janc18/CAE32/Source_code/Interfaz_grafica/Interfaz_gtk/src_images/Volante2.png

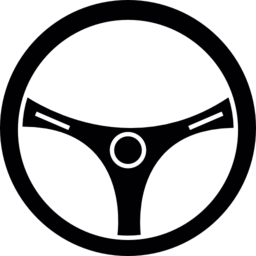
Source_code/Interfaz_grafica/Interfaz_gtk/src_images/Volante2.png
