janc18/CAE32/UML/UML_png_files/Use_cases_CAE32.png

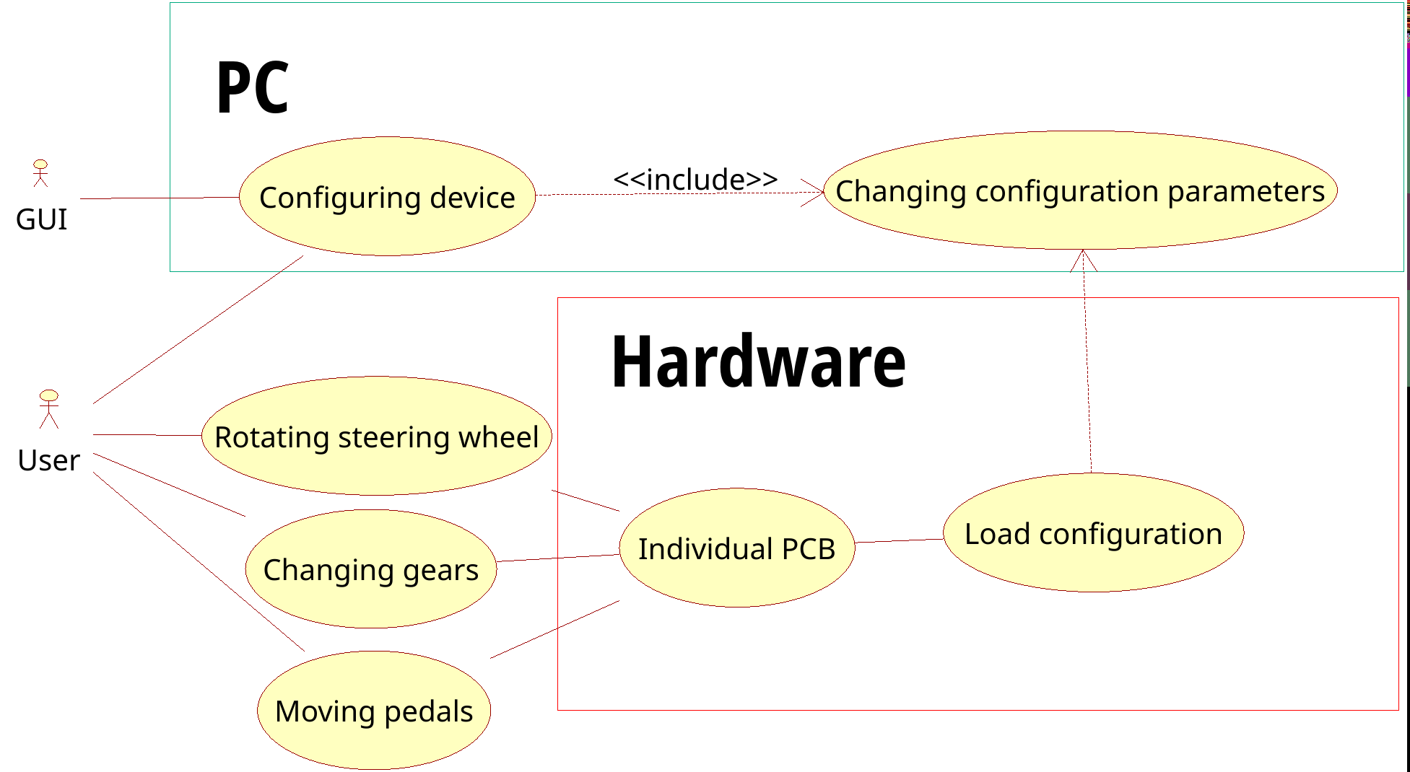
UML/UML_png_files/Use_cases_CAE32.png
