janc18/CAE32/Source_code/blink/Core/Inc/main.h

#define CS_Pin GPIO_PIN_4
#define CS_GPIO_Port GPIOA
#define SCLK_Pin GPIO_PIN_5
#define SCLK_GPIO_Port GPIOA
#define MISO_Pin GPIO_PIN_6
#define MISO_GPIO_Port GPIOA
#define MOSI_Pin GPIO_PIN_7
#define MOSI_GPIO_Port GPIOA
