janc18/CAE32/Source_code/blink/Core/Src/main.c

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
/* Includes ------------------------------------------------------------------*/
#include "main.h"
#include "usb_device.h"

/* USER CODE BEGIN Includes */
#include "usbd_hid.h"
#include "i2cDriver.h"
#include "initialization.h"
/* USER CODE END Includes */


/* USER CODE BEGIN PV */
extern USBD_HandleTypeDef hUsbDeviceFS;
uint16_t rawAcceleratorValue=0;
uint16_t rawClutchValue=0;
uint16_t rawBrakeValue=0;
uint8_t acceleratorChannel=1;
uint8_t clutchChannel=2;
uint8_t brakeChannel=4;
/* USER CODE END PV */

void SystemClock_Config(void);
static void MX_GPIO_Init(void);
/**
  * @brief  The application entry point.
  * @retval int
  */
int main(void)
{

  /* MCU Configuration--------------------------------------------------------*/

  /* Reset of all peripherals, Initializes the Flash interface and the Systick. */
  HAL_Init();

  /* Configure the system clock */
  SystemClock_Config();

  /* Initialize all configured peripherals */
  MX_GPIO_Init();
  MX_USB_DEVICE_Init();
  /* Infinite loop */
  /* USER CODE BEGIN WHILE */
	while (1) {
		rawAcceleratorValue = ADC128S102_ReadSingleChannel(acceleratorChannel);
		rawBrakeValue=ADC128S102_ReadSingleChannel(brakeChannel);
		rawClutchValue=ADC128S102_ReadSingleChannel(clutchChannel);
		uint8_t mapAcceleratorValue = map(rawAcceleratorValue, 0, 3750, 0, 255);
		uint8_t mapBrakeValue = map(rawBrakeValue, 0, 3750, 0, 255);
		uint8_t mapClutchValue = map(rawClutchValue, 0, 3750, 0, 255);
		sendAxisValues(hUsbDeviceFS, mapAcceleratorValue, mapClutchValue, mapBrakeValue);
		/* USER CODE END WHILE */

    /* USER CODE BEGIN 3 */

	}
  /* USER CODE END 3 */
}

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
